irishrain/gervifonn/case/gervifonn_bottom.png

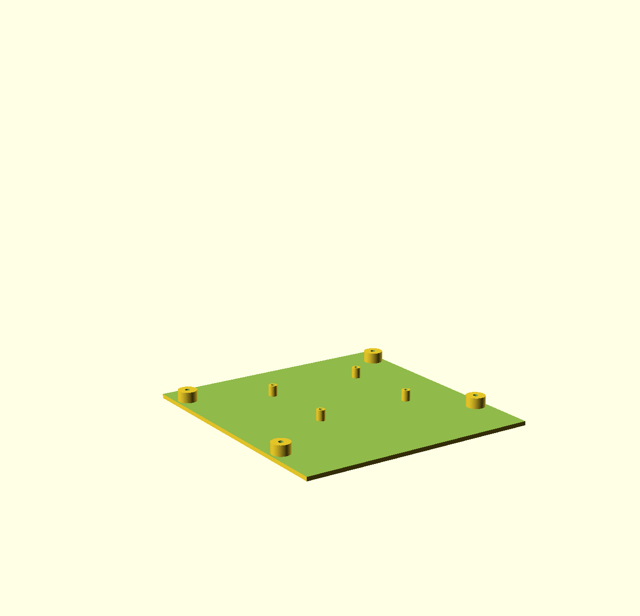
case/gervifonn_bottom.png
