irishrain/gervifonn/case/gervifonn_right.png

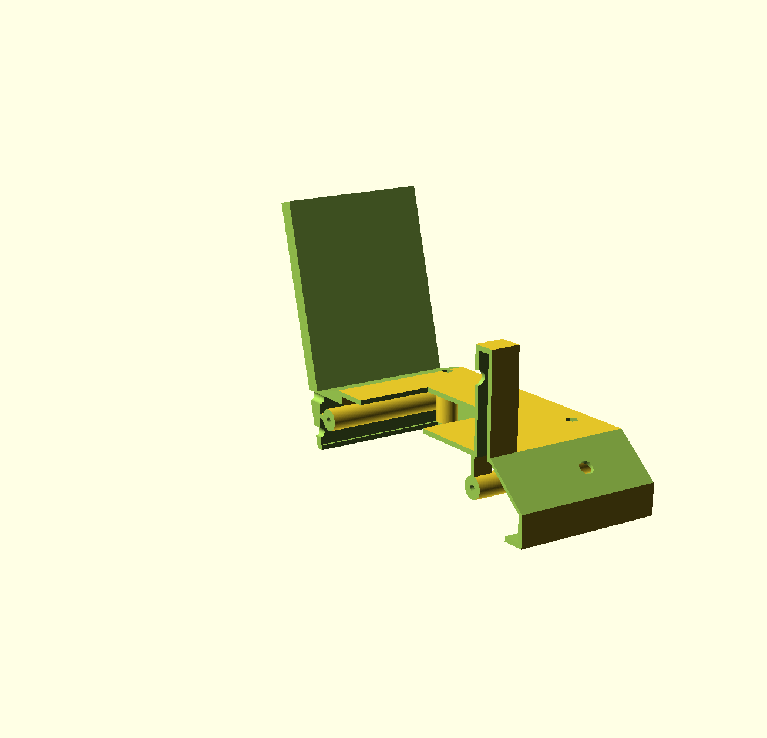
case/gervifonn_right.png
